daimik/Esphome-Load-Sensing-Relay/img/3.jpeg

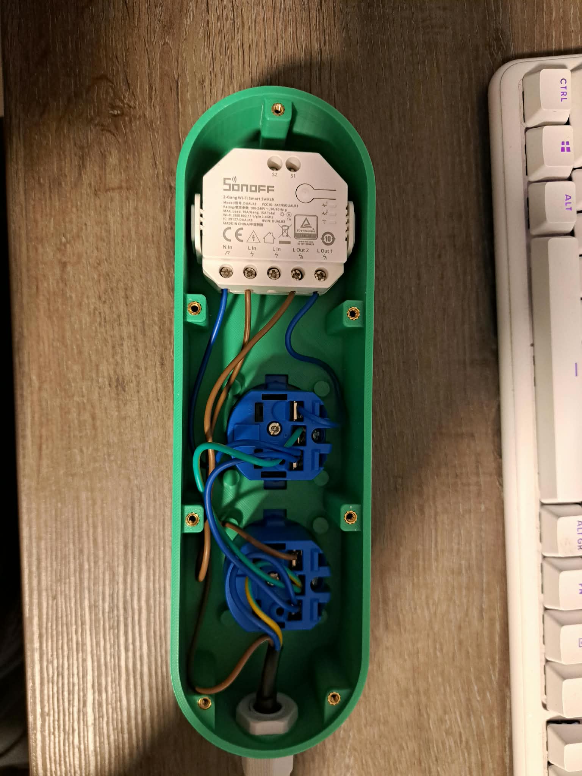
img/3.jpeg
